reivaxy/miniCommodore/resources/20190321_224756.jpg

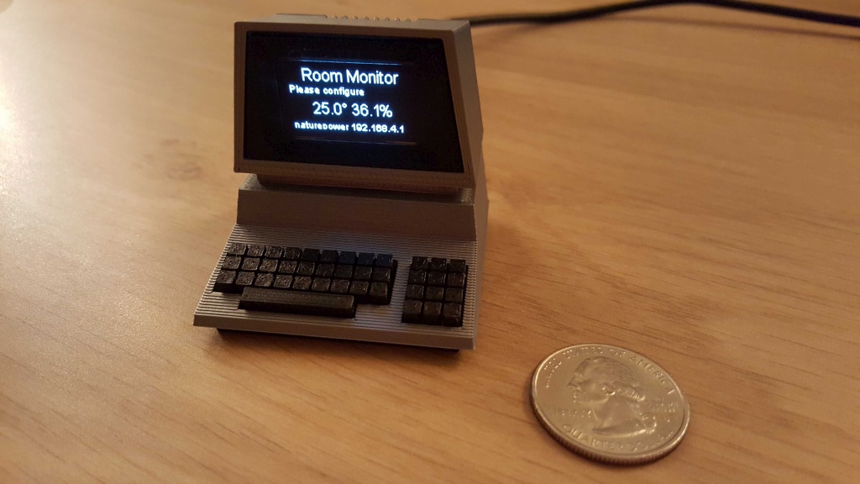
resources/20190321_224756.jpg
