reivaxy/miniCommodore/resources/20190322_075943.jpg

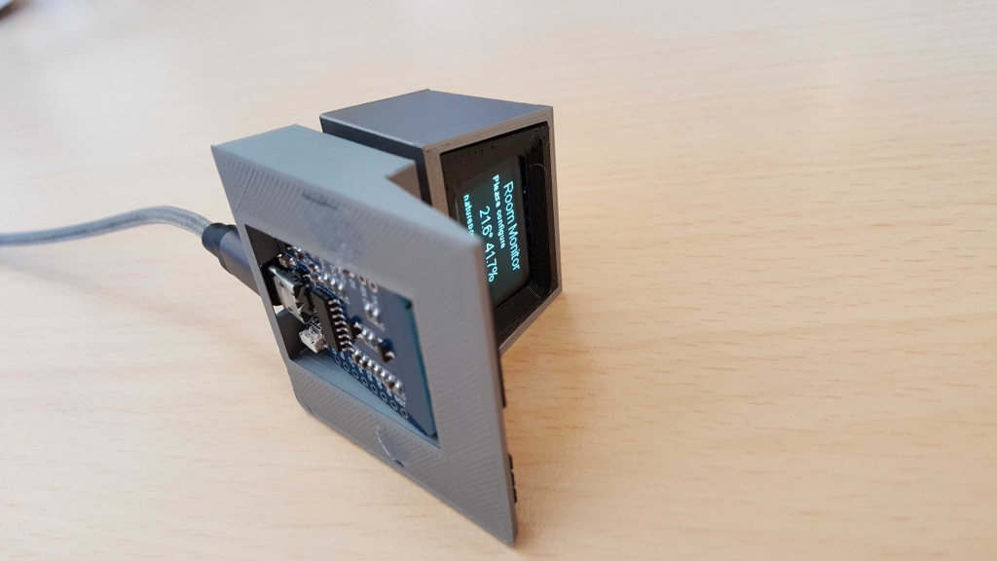
resources/20190322_075943.jpg
