reivaxy/miniCommodore/resources/20190322_080031.jpg

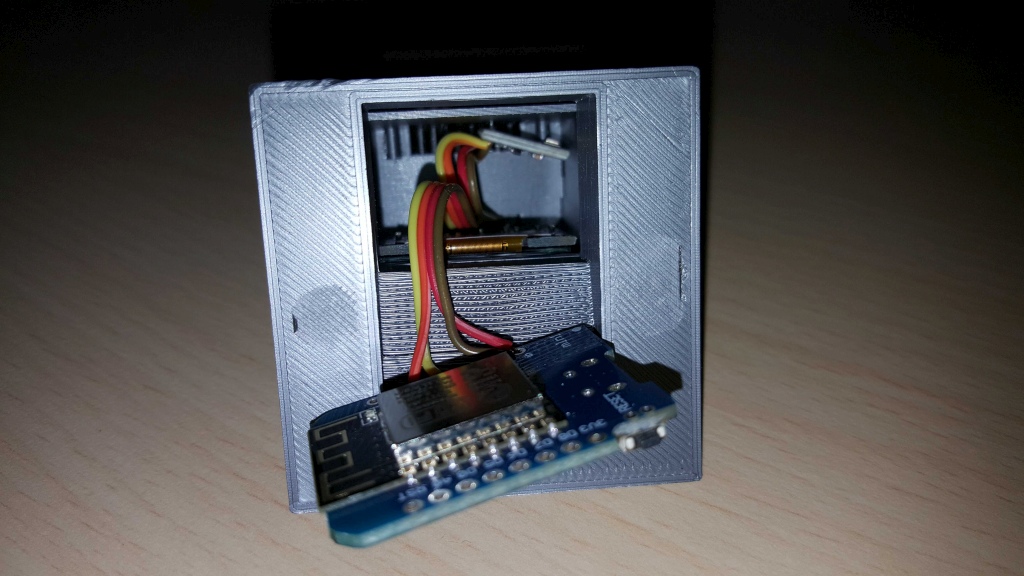
resources/20190322_080031.jpg
